404background/RumiCar-C3/Fusion360/出力上面.jpg

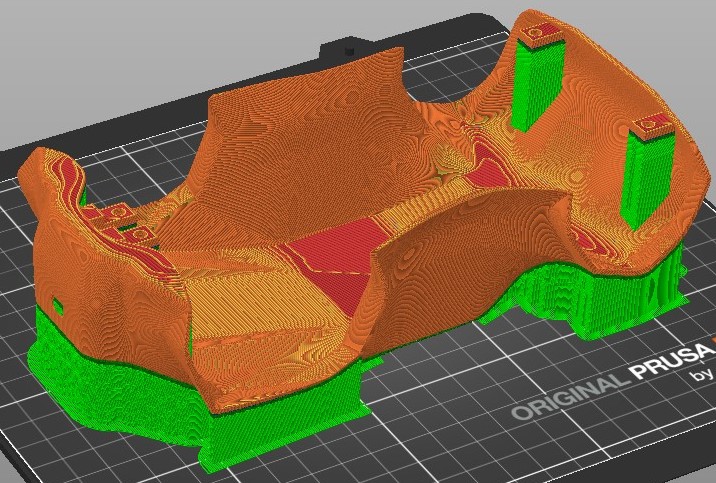
Fusion360/出力上面.jpg
