404background/RumiCar-C3/Fusion360/車体背面.jpg

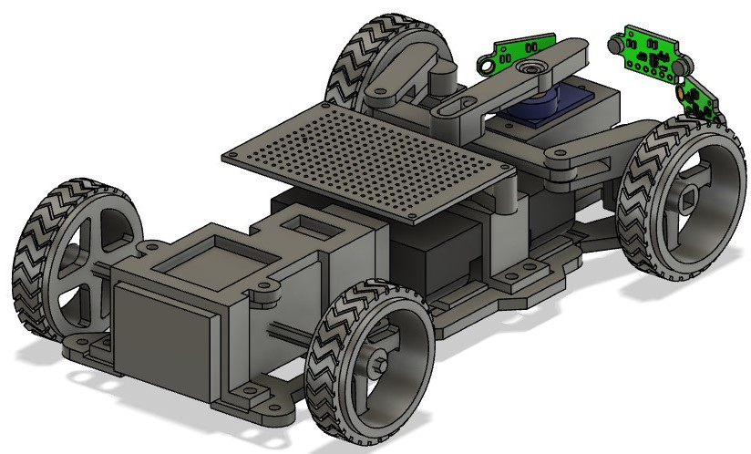
Fusion360/車体背面.jpg
