404background/RumiCar-C3/Fusion360/車体裏面.jpg

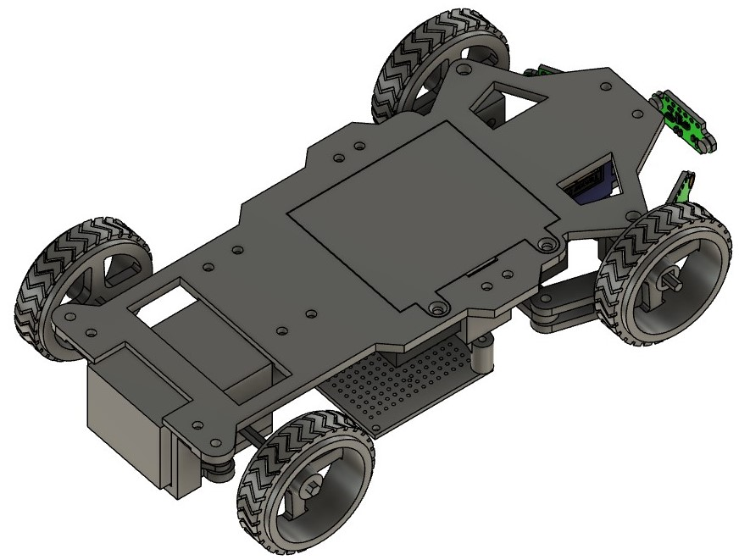
Fusion360/車体裏面.jpg
